MOSH-Insa-Toulouse/2025-2026-4GP-FRANCOISE-MAS/LTSPICE/Filtre.asc

C1: cap; 100n
C2: cap; 100n
C4: cap; 1µ
C5: cap; 10p
R1: res; 100k
R2: res; 1k
R3: res; 100k
R5: res; 10k
R6: res; 1k
U1: LTC1050
V1: voltage; 5
V2: voltage; SINE(0 325 50)
V3: voltage; PULSE(0 1 0.2 0.1 0.1 2)
X1: capteur
Named nets: 0, ADC
.tran 5
;ac dec 4 1 1G
;param G0 10n
;param G1 10n
;param R1 100k
